overset/trackball/pictures/20221221-PCB-3D-v03-front-SMD.jpg

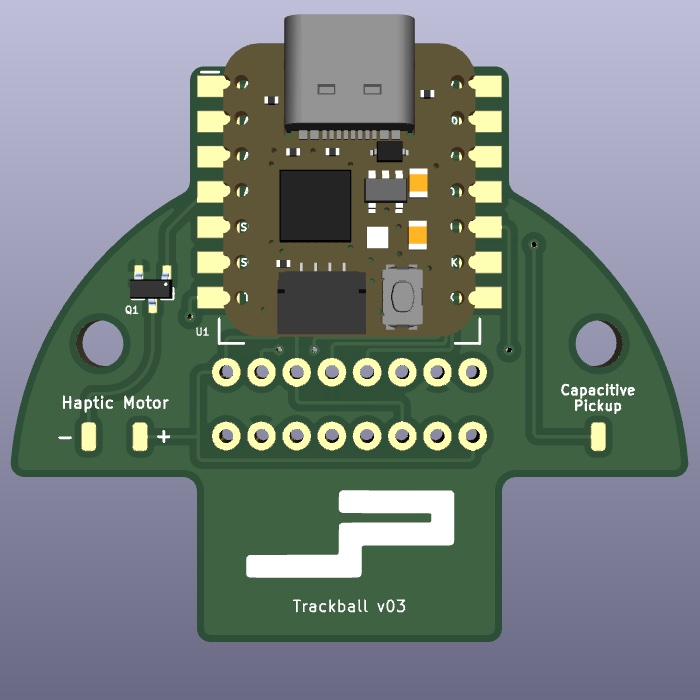
pictures/20221221-PCB-3D-v03-front-SMD.jpg
