overset/trackball/pictures/20221221-PCB-editor-v03-front.jpg

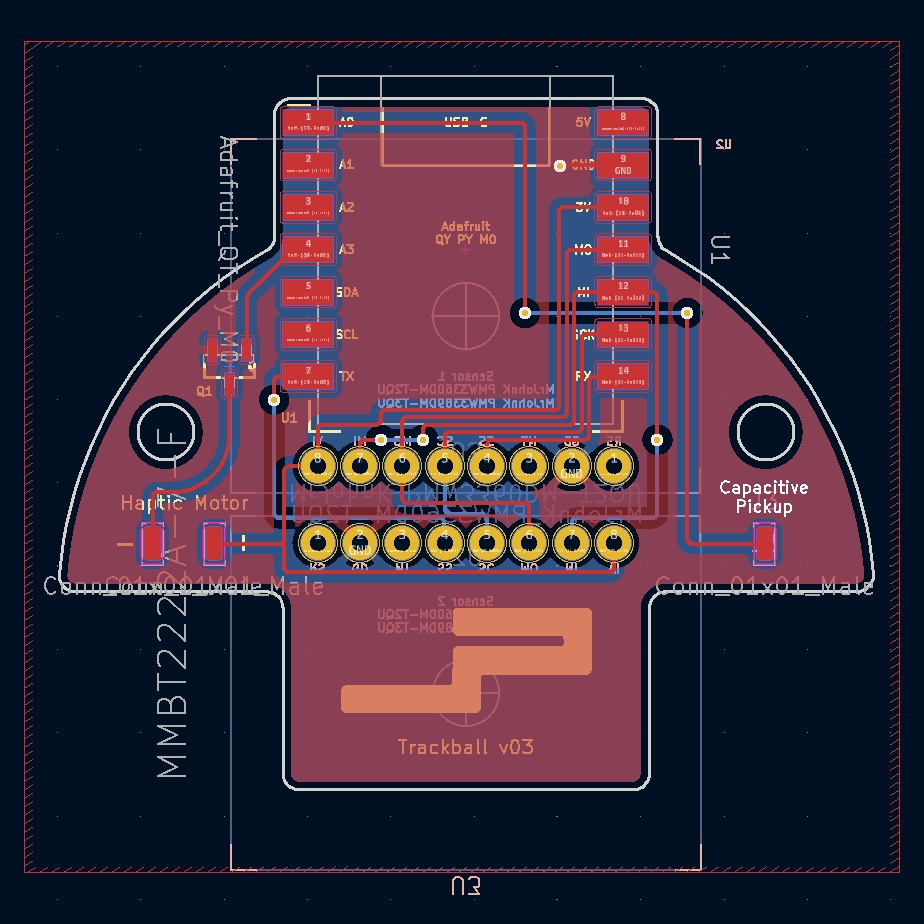
pictures/20221221-PCB-editor-v03-front.jpg
